Etienne248/Bluetooth_Ultrasonic_Speaker/images/components1.jpg

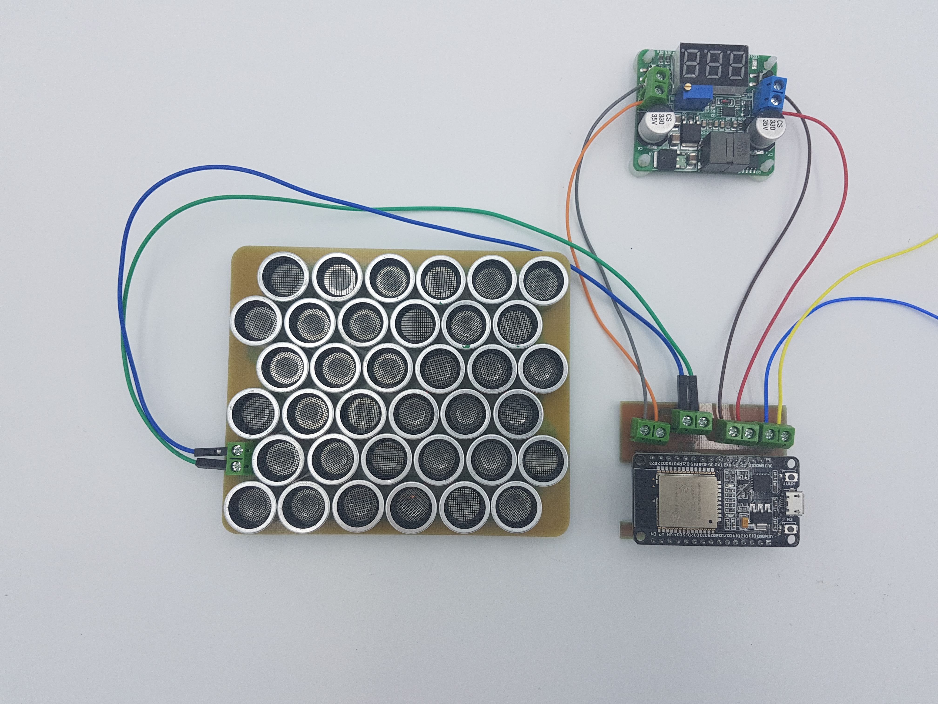
images/components1.jpg
