Etienne248/Bluetooth_Ultrasonic_Speaker/images/SolderMaskTemplate.jpg

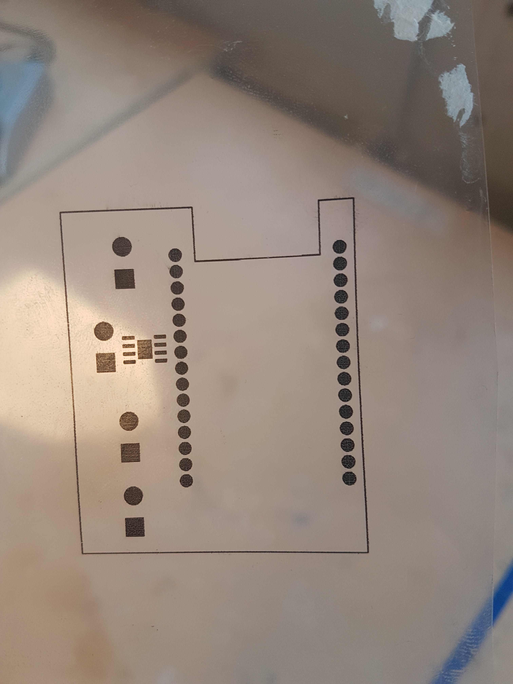
images/SolderMaskTemplate.jpg
