Etienne248/Bluetooth_Ultrasonic_Speaker/images/withSolderMaskTemplate.jpg

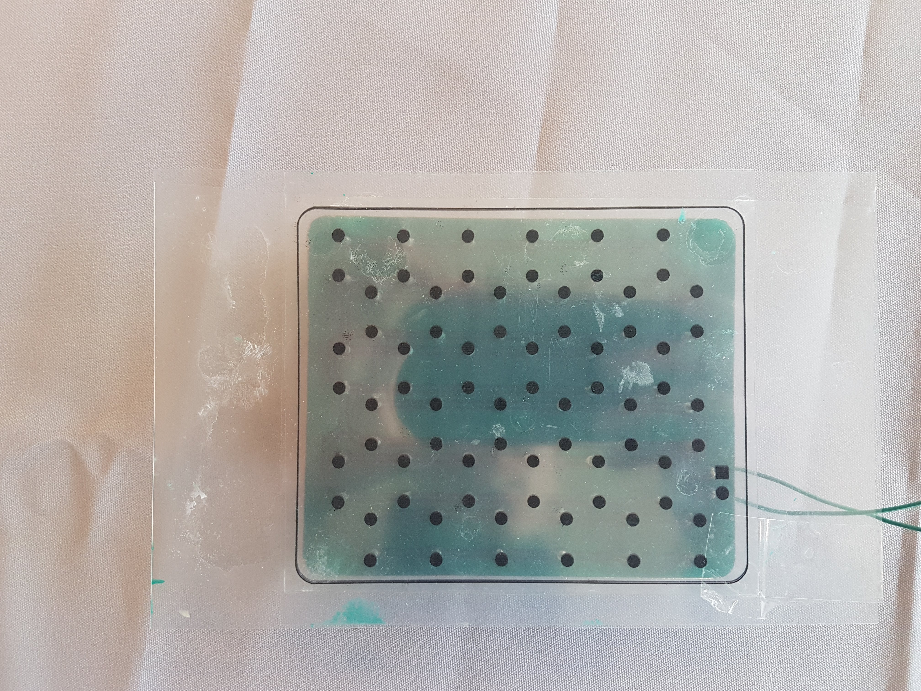
images/withSolderMaskTemplate.jpg
