Etienne248/Bluetooth_Ultrasonic_Speaker/Code_Ultrasonic_Speaker_esp_idf/src/bt_app_core.c

/*
 * SPDX-FileCopyrightText: 2021-2022 Espressif Systems (Shanghai) CO LTD
 *
 * SPDX-License-Identifier: Unlicense OR CC0-1.0
 */
#include "glob_var.h"

#include <stdint.h>
#include <string.h>
#include <stdbool.h>
#include "freertos/xtensa_api.h"
#include "freertos/FreeRTOSConfig.h"
#include "freertos/FreeRTOS.h"
#include "freertos/queue.h"
#include "freertos/task.h"
#include "esp_log.h"
#include "bt_app_core.h"
#ifdef CONFIG_EXAMPLE_A2DP_SINK_OUTPUT_INTERNAL_DAC
// DAC DMA mode is only supported by the legacy I2S driver, it will be replaced once DAC has its own DMA dirver
#include "driver/i2s.h"
#else
#include "driver/i2s_std.h"
#endif
#include "freertos/ringbuf.h"

/*******************************
 * STATIC FUNCTION DECLARATIONS
 ******************************/

/* handler for application task */
static void bt_app_task_handler(void *arg);
/* handler for I2S task */
static void bt_i2s_task_handler(void *arg);
/* message sender */
static bool bt_app_send_msg(bt_app_msg_t *msg);
/* handle dispatched messages */
static void bt_app_work_dispatched(bt_app_msg_t *msg);

/*******************************
 * STATIC VARIABLE DEFINITIONS
 ******************************/

static QueueHandle_t s_bt_app_task_queue = NULL;  /* handle of work queue */
static TaskHandle_t s_bt_app_task_handle = NULL;  /* handle of application task  */
static TaskHandle_t s_bt_i2s_task_handle = NULL;  /* handle of I2S task */
static RingbufHandle_t s_ringbuf_i2s = NULL;     /* handle of ringbuffer for I2S */
#ifndef CONFIG_EXAMPLE_A2DP_SINK_OUTPUT_INTERNAL_DAC
extern i2s_chan_handle_t tx_chan;
#endif

/*******************************
 * STATIC FUNCTION DEFINITIONS
 ******************************/

static bool bt_app_send_msg(bt_app_msg_t *msg)
{
    if (msg == NULL) {
        return false;
    }

    /* send the message to work queue */
    if (xQueueSend(s_bt_app_task_queue, msg, 10 / portTICK_PERIOD_MS) != pdTRUE) {
        ESP_LOGE(BT_APP_CORE_TAG, "%s xQueue send failed", __func__);
        return false;
    }
    return true;
}

static void bt_app_work_dispatched(bt_app_msg_t *msg)
{
    if (msg->cb) {
        msg->cb(msg->event, msg->param);
    }
}

static void bt_app_task_handler(void *arg)
{
    bt_app_msg_t msg;

    for (;;) {
        /* receive message from work queue and handle it */
        if (pdTRUE == xQueueReceive(s_bt_app_task_queue, &msg, (TickType_t)portMAX_DELAY)) {
            ESP_LOGD(BT_APP_CORE_TAG, "%s, signal: 0x%x, event: 0x%x", __func__, msg.sig, msg.event);

            switch (msg.sig) {
            case BT_APP_SIG_WORK_DISPATCH:
                bt_app_work_dispatched(&msg);
                break;
            default:
                ESP_LOGW(BT_APP_CORE_TAG, "%s, unhandled signal: %d", __func__, msg.sig);
                break;
            } /* switch (msg.sig) */

            if (msg.param) {
                free(msg.param);
            }
        }
    }
}

static void bt_i2s_task_handler(void *arg)
{
    uint8_t *data = NULL;
    size_t item_size = 0;
    size_t bytes_written = 0;

    for (;;) {
        /* receive data from ringbuffer and write it to I2S DMA transmit buffer */
        data = (uint8_t *)xRingbufferReceive(s_ringbuf_i2s, &item_size, (TickType_t)portMAX_DELAY);
        if (item_size != 0){
            xRingbufferSend(ringbuf_pwm, data, item_size, 1);
        #ifdef CONFIG_EXAMPLE_A2DP_SINK_OUTPUT_INTERNAL_DAC
            i2s_write(0, data, item_size, &bytes_written, portMAX_DELAY);
        #else
            i2s_channel_write(tx_chan, data, item_size, &bytes_written, portMAX_DELAY);
        #endif
            vRingbufferReturnItem(s_ringbuf_i2s, (void *)data);
        }
    }
}

/********************************
 * EXTERNAL FUNCTION DEFINITIONS
 *******************************/

bool bt_app_work_dispatch(bt_app_cb_t p_cback, uint16_t event, void *p_params, int param_len, bt_app_copy_cb_t p_copy_cback)
{
    ESP_LOGD(BT_APP_CORE_TAG, "%s event: 0x%x, param len: %d", __func__, event, param_len);

    bt_app_msg_t msg;
    memset(&msg, 0, sizeof(bt_app_msg_t));

    msg.sig = BT_APP_SIG_WORK_DISPATCH;
    msg.event = event;
    msg.cb = p_cback;

    if (param_len == 0) {
        return bt_app_send_msg(&msg);
    } else if (p_params && param_len > 0) {
        if ((msg.param = malloc(param_len)) != NULL) {
            memcpy(msg.param, p_params, param_len);
            /* check if caller has provided a copy callback to do the deep copy */
            if (p_copy_cback) {
                p_copy_cback(msg.param, p_params, param_len);
            }
            return bt_app_send_msg(&msg);
        }
    }

    return false;
}

void bt_app_task_start_up(void)
{
    s_bt_app_task_queue = xQueueCreate(10, sizeof(bt_app_msg_t));
    xTaskCreate(bt_app_task_handler, "BtAppTask", 3072, NULL, 10, &s_bt_app_task_handle);
}

void bt_app_task_shut_down(void)
{
    if (s_bt_app_task_handle) {
        vTaskDelete(s_bt_app_task_handle);
        s_bt_app_task_handle = NULL;
    }
    if (s_bt_app_task_queue) {
        vQueueDelete(s_bt_app_task_queue);
        s_bt_app_task_queue = NULL;
    }
}

void bt_i2s_task_start_up(void)
{
    if ((s_ringbuf_i2s = xRingbufferCreate(8 * 1024, RINGBUF_TYPE_BYTEBUF)) == NULL) {
        return;
    }
    xTaskCreate(bt_i2s_task_handler, "BtI2STask", 1024, NULL, configMAX_PRIORITIES - 3, &s_bt_i2s_task_handle);
}

void bt_i2s_task_shut_down(void)
{
    if (s_bt_i2s_task_handle) {
        vTaskDelete(s_bt_i2s_task_handle);
        s_bt_i2s_task_handle = NULL;
    }
    if (s_ringbuf_i2s) {
        vRingbufferDelete(s_ringbuf_i2s);
        s_ringbuf_i2s = NULL;
    }
}

size_t write_ringbuf(const uint8_t *data, size_t size)
{
    BaseType_t done = xRingbufferSend(s_ringbuf_i2s, (void *)data, size, (TickType_t)portMAX_DELAY);

    return done ? size : 0;
}
